Matt-Pettit/EEE3088F-Project/Design-files/Power Circuit.asc

Battery: voltage; 4.2
D1: schottky
D2: schottky
M1: pmos
R1: res; 10000
R2: res; 5000
USB: voltage; 5
Named nets: 0
.tran 500
